74hc595/Numitron-Clock/code/version.h

#ifndef VERSION_H_
#define VERSION_H_

#define FIRMWARE_VERSION_MAJOR 1
#define FIRMWARE_VERSION_MINOR 2

/**
 * In "programmer mode" the bootloader can be entered by holding the top button
 * when the time or date is showing.
 */
#define PROGRAMMER_MODE 0

#endif
